anventia/TKLC-Mechanical-Keyboard/TKLC_v1/resources/led_wiring.png

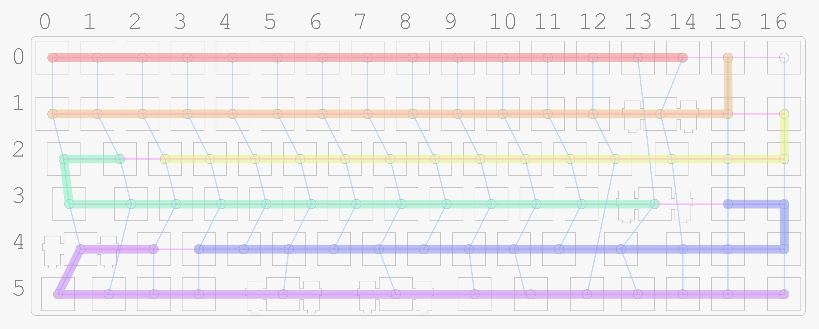
TKLC_v1/resources/led_wiring.png
